Zachary-Levesque/Smart-Flood-Detection-System/firmware/main/sensor_logic.h

#pragma once

#include <stdbool.h>

#include "app_config.h"

typedef struct {
    int consecutive_wet_samples;
    system_event_t last_reported_state;
} sensor_debounce_state_t;

static inline bool sensor_level_is_wet(int level_percent, int threshold_percent)
{
    return level_percent >= threshold_percent;
}

void sensor_debounce_init(sensor_debounce_state_t *state);
system_event_t sensor_debounce_update(sensor_debounce_state_t *state,
                                      int level_percent,
                                      int threshold_percent,
                                      int required_samples,
                                      bool *changed);
